biomurph/DINACON_Hummingbird_Heartbeats/2019/HummingBirdHeartbeats_01.JPG

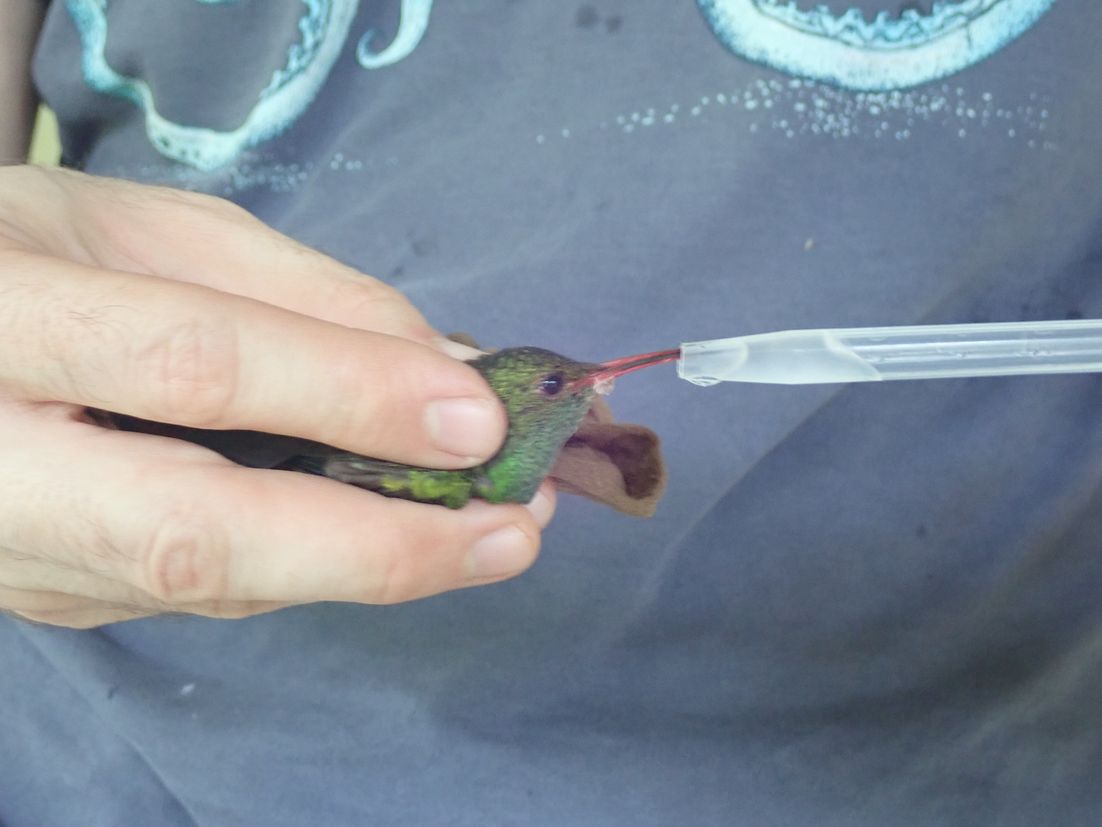
2019/HummingBirdHeartbeats_01.JPG
