biomurph/DINACON_Hummingbird_Heartbeats/2019/HummingBirdHeartbeats_02.JPG

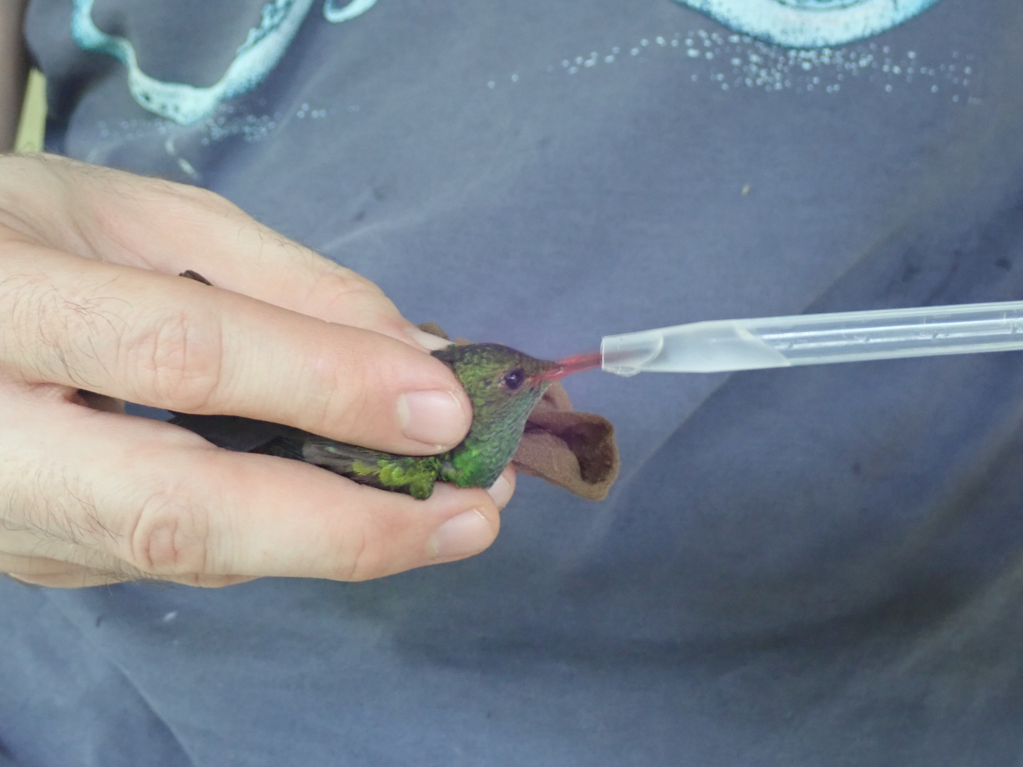
2019/HummingBirdHeartbeats_02.JPG
