biomurph/DINACON_Hummingbird_Heartbeats/2019/HummingBirdHeartbeats_03.JPG

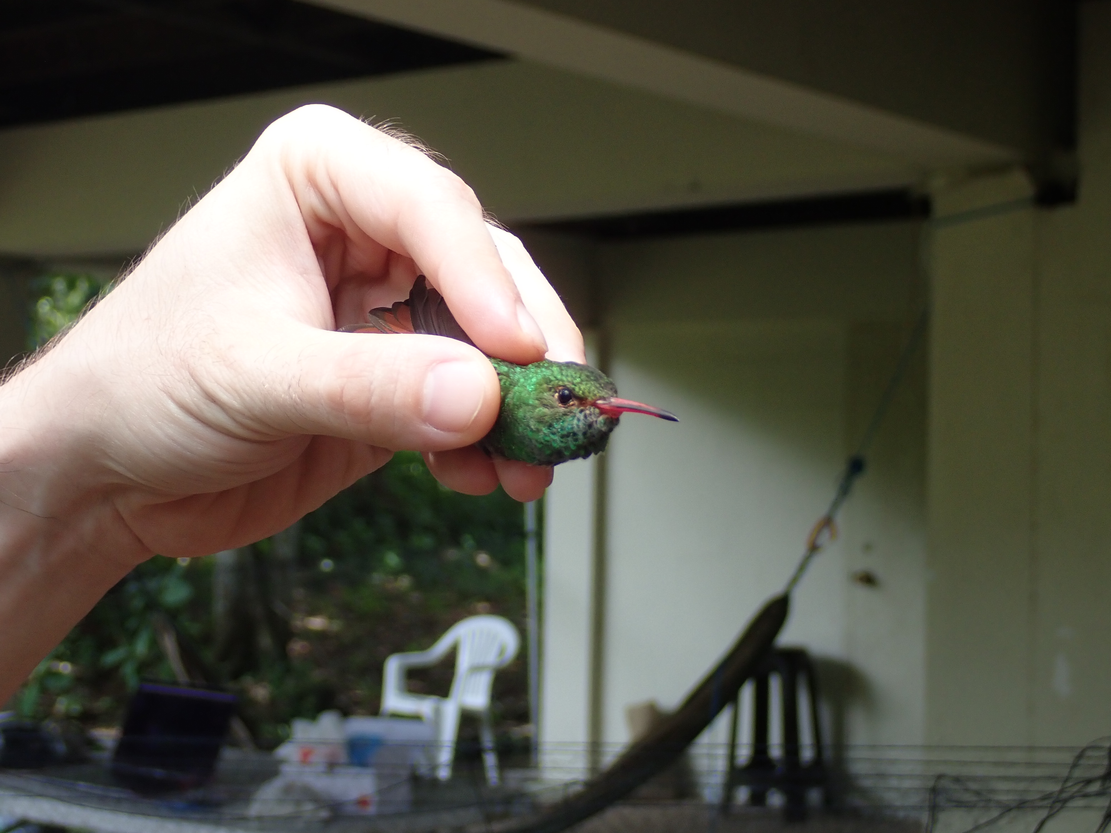
2019/HummingBirdHeartbeats_03.JPG
