biomurph/DINACON_Hummingbird_Heartbeats/2019/HummingBirdHeartbeats_04.JPG

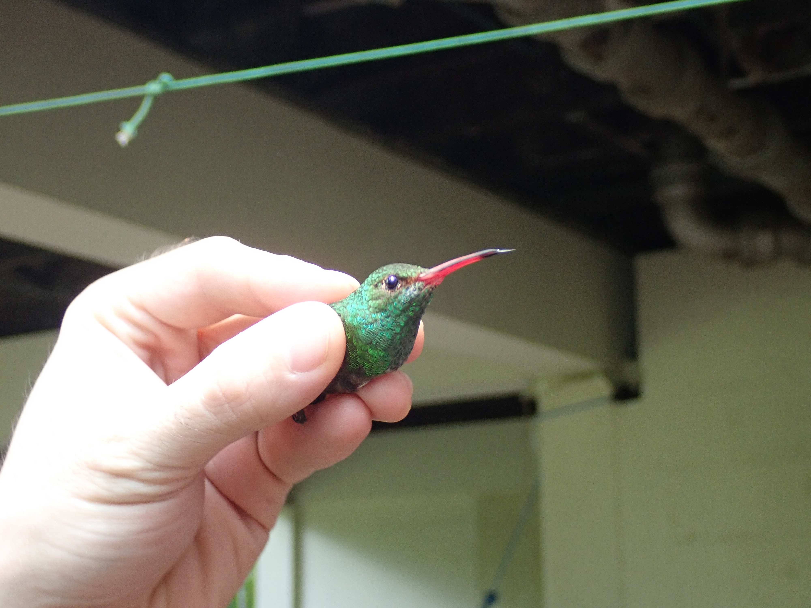
2019/HummingBirdHeartbeats_04.JPG
