biomurph/DINACON_Hummingbird_Heartbeats/2019/HummingBirdHeartbeats_05.JPG

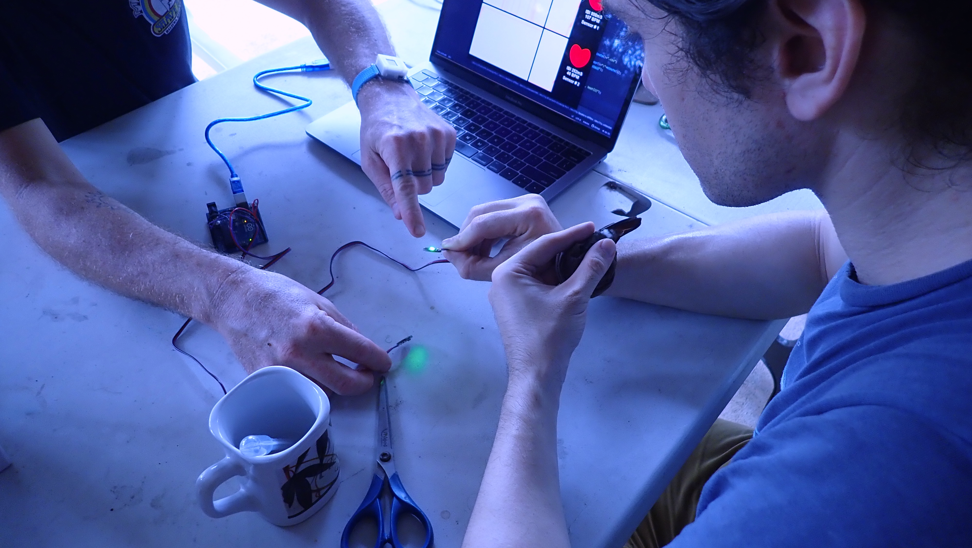
2019/HummingBirdHeartbeats_05.JPG
