biomurph/DINACON_Hummingbird_Heartbeats/2019/HummingBirdHeartbeats_09.JPG

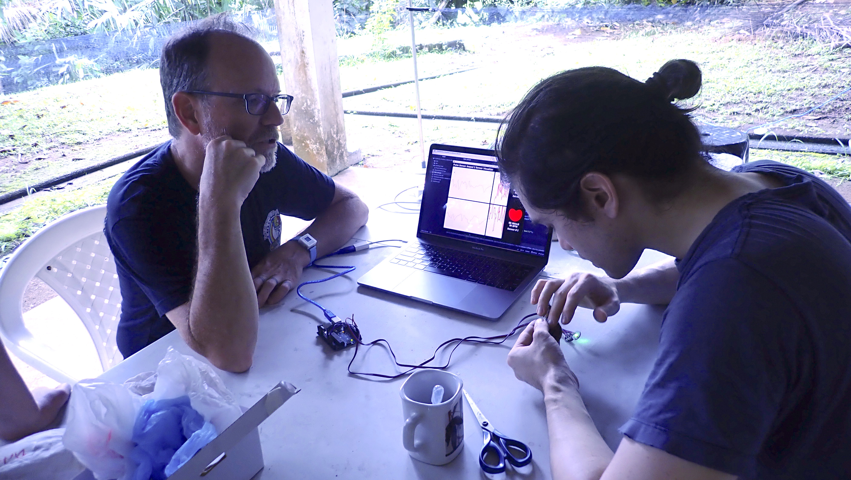
2019/HummingBirdHeartbeats_09.JPG
