biomurph/DINACON_Hummingbird_Heartbeats/2019/HummingBirdHeartbeats_10.JPG

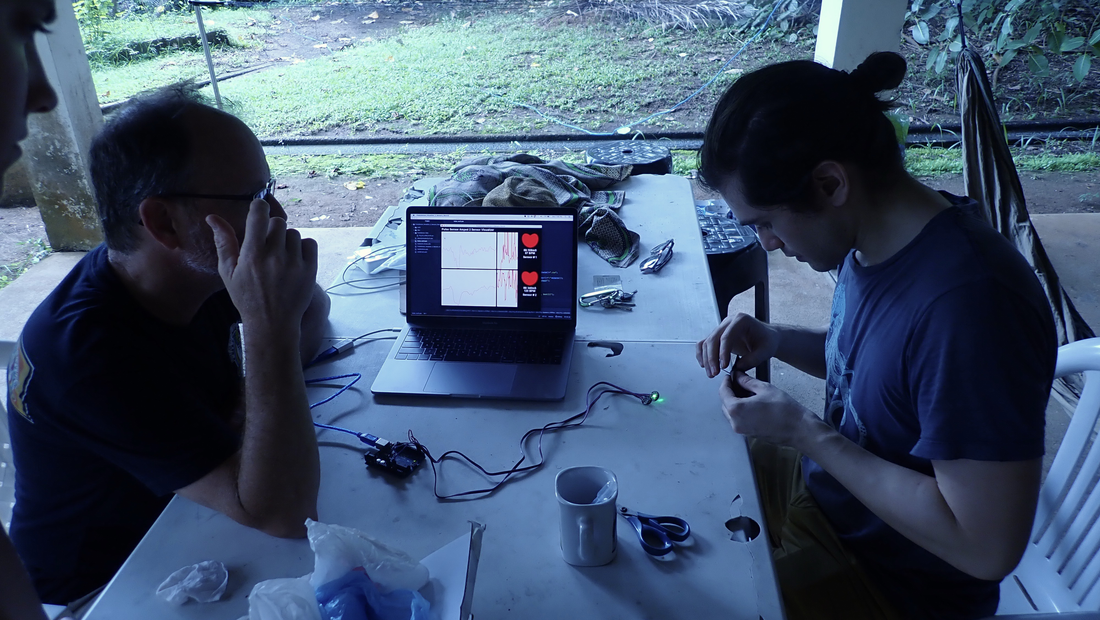
2019/HummingBirdHeartbeats_10.JPG
