biomurph/DINACON_Hummingbird_Heartbeats/2019/HummingBirdHeartbeats_12.JPG

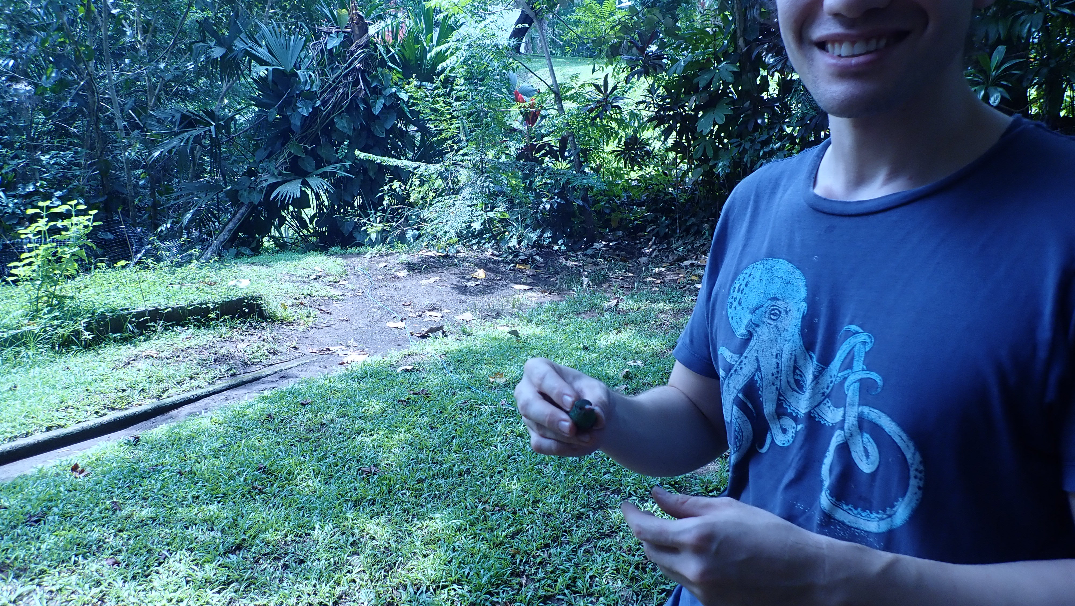
2019/HummingBirdHeartbeats_12.JPG
