biomurph/DINACON_Hummingbird_Heartbeats/2019/HummingBirdHeartbeats_15.JPG

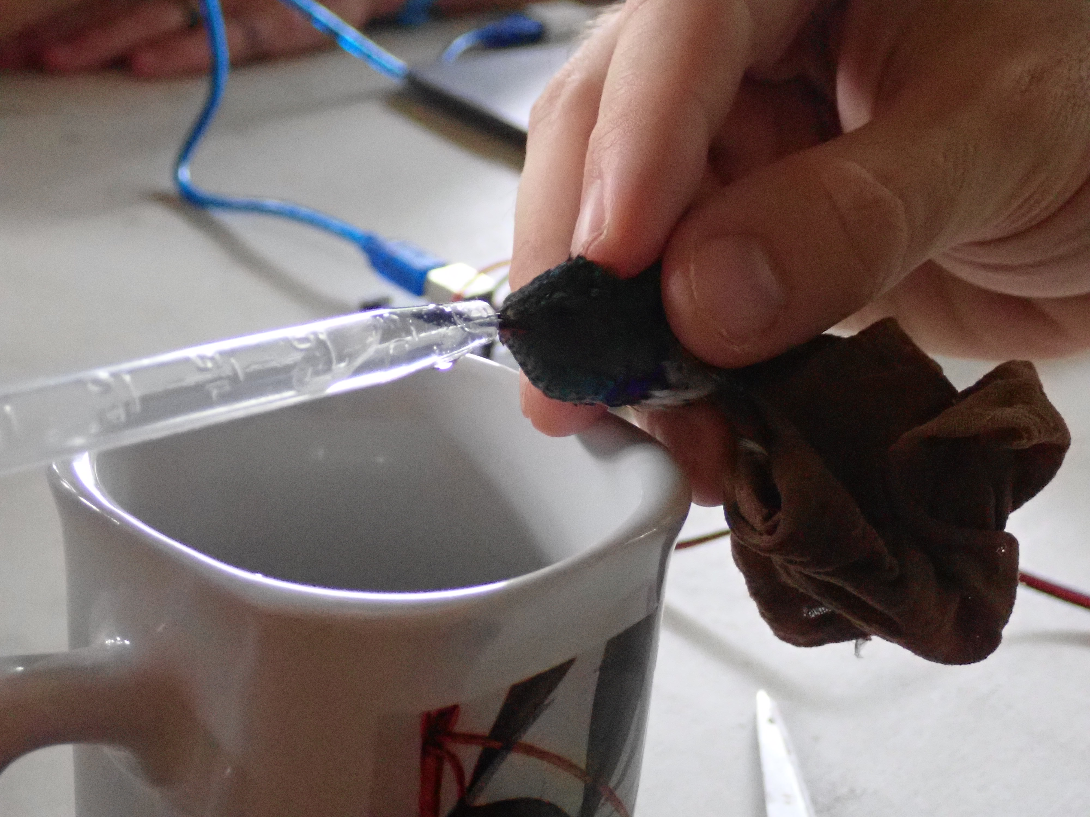
2019/HummingBirdHeartbeats_15.JPG
