biomurph/DINACON_Hummingbird_Heartbeats/2019/HummingBirdHeartbeats_16.JPG

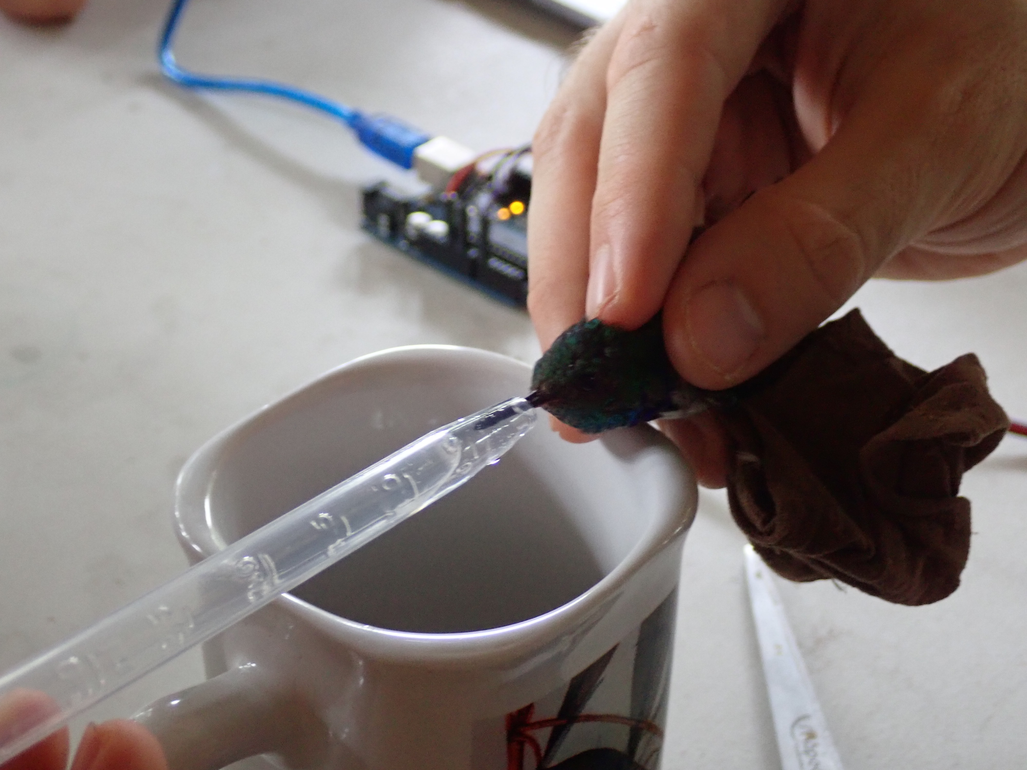
2019/HummingBirdHeartbeats_16.JPG
