biomurph/DINACON_Hummingbird_Heartbeats/2019/HummingBirdHeartbeats_19.JPG

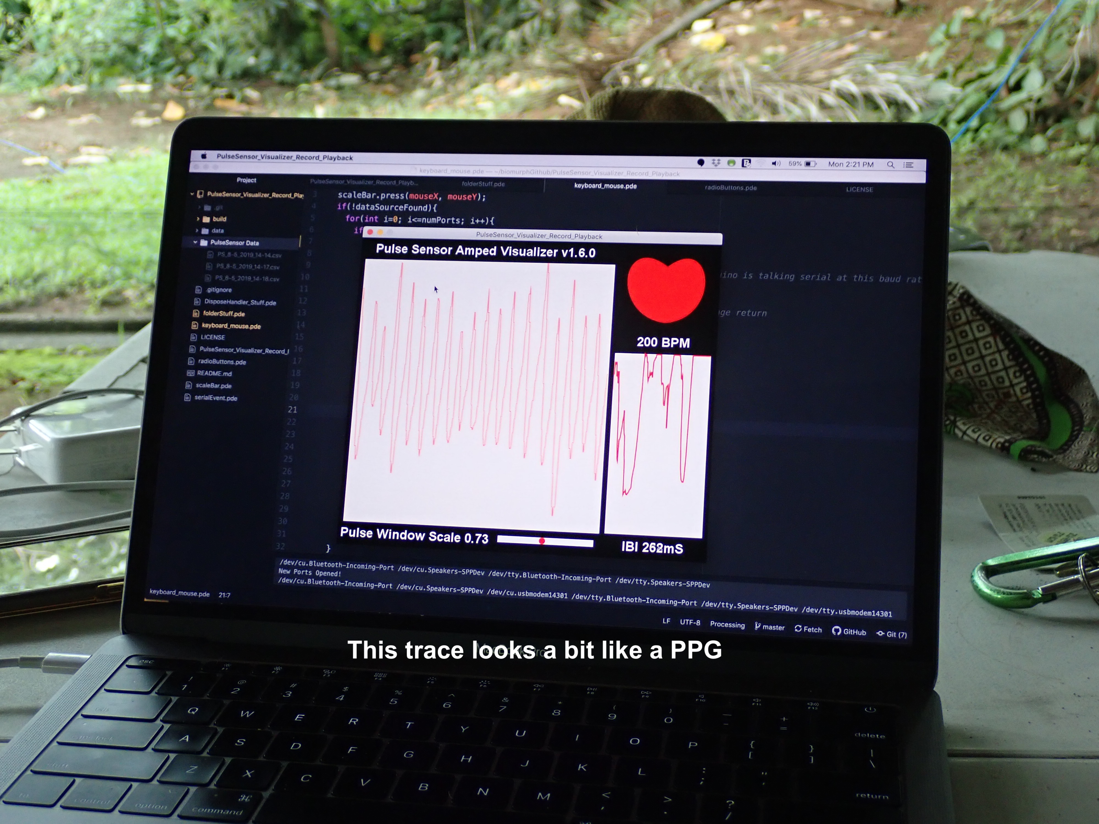
2019/HummingBirdHeartbeats_19.JPG
