biomurph/DINACON_Hummingbird_Heartbeats/2019/HummingBirdHeartbeats_20.JPG

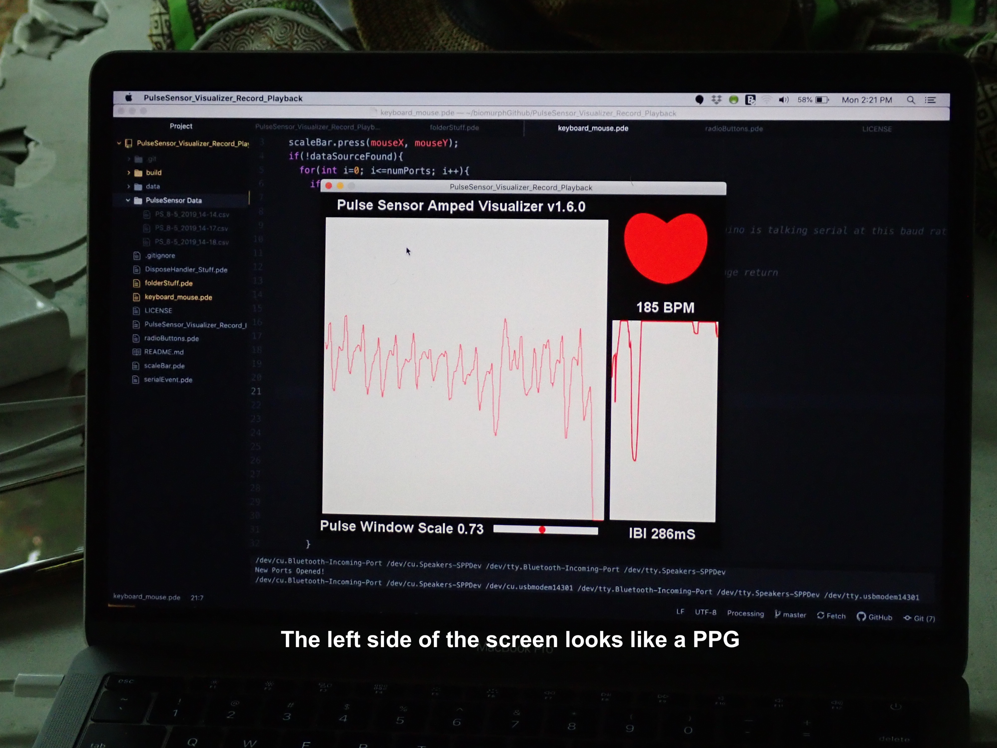
2019/HummingBirdHeartbeats_20.JPG
