biomurph/DINACON_Hummingbird_Heartbeats/2019/HummingBirdHeartbeats_22.JPG

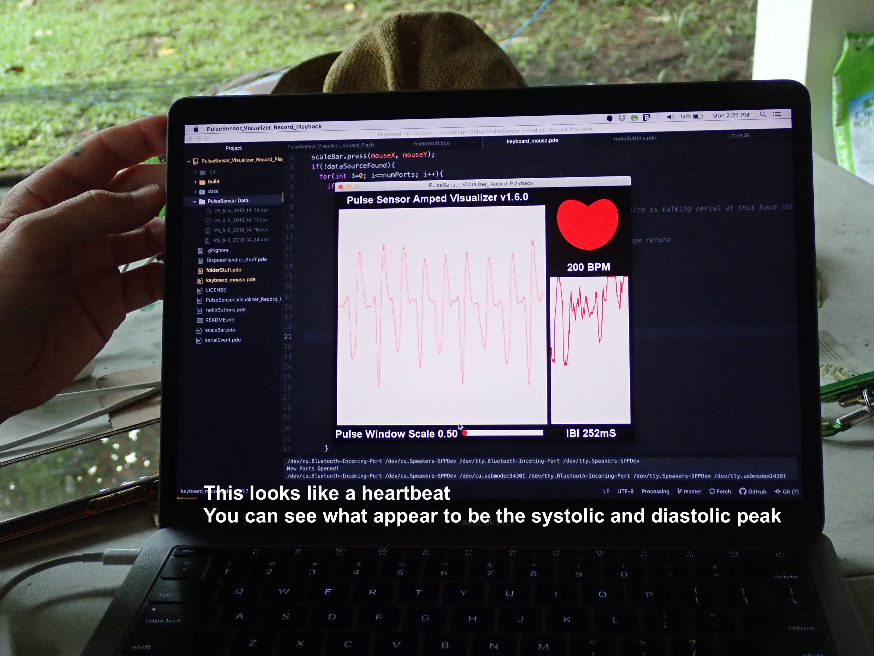
2019/HummingBirdHeartbeats_22.JPG
