biomurph/DINACON_Hummingbird_Heartbeats/2019/IMG_20190805_141204.jpg

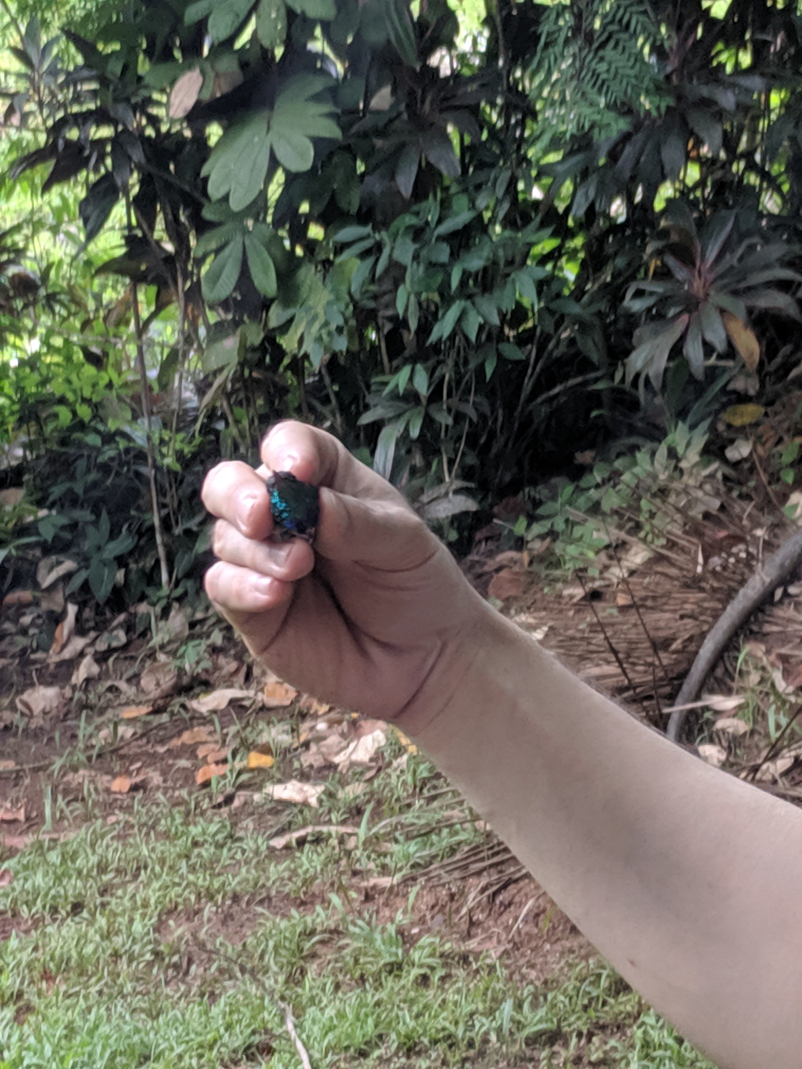
2019/IMG_20190805_141204.jpg
