biomurph/DINACON_Hummingbird_Heartbeats/2022/Data/1st_attempts/boto_01.png

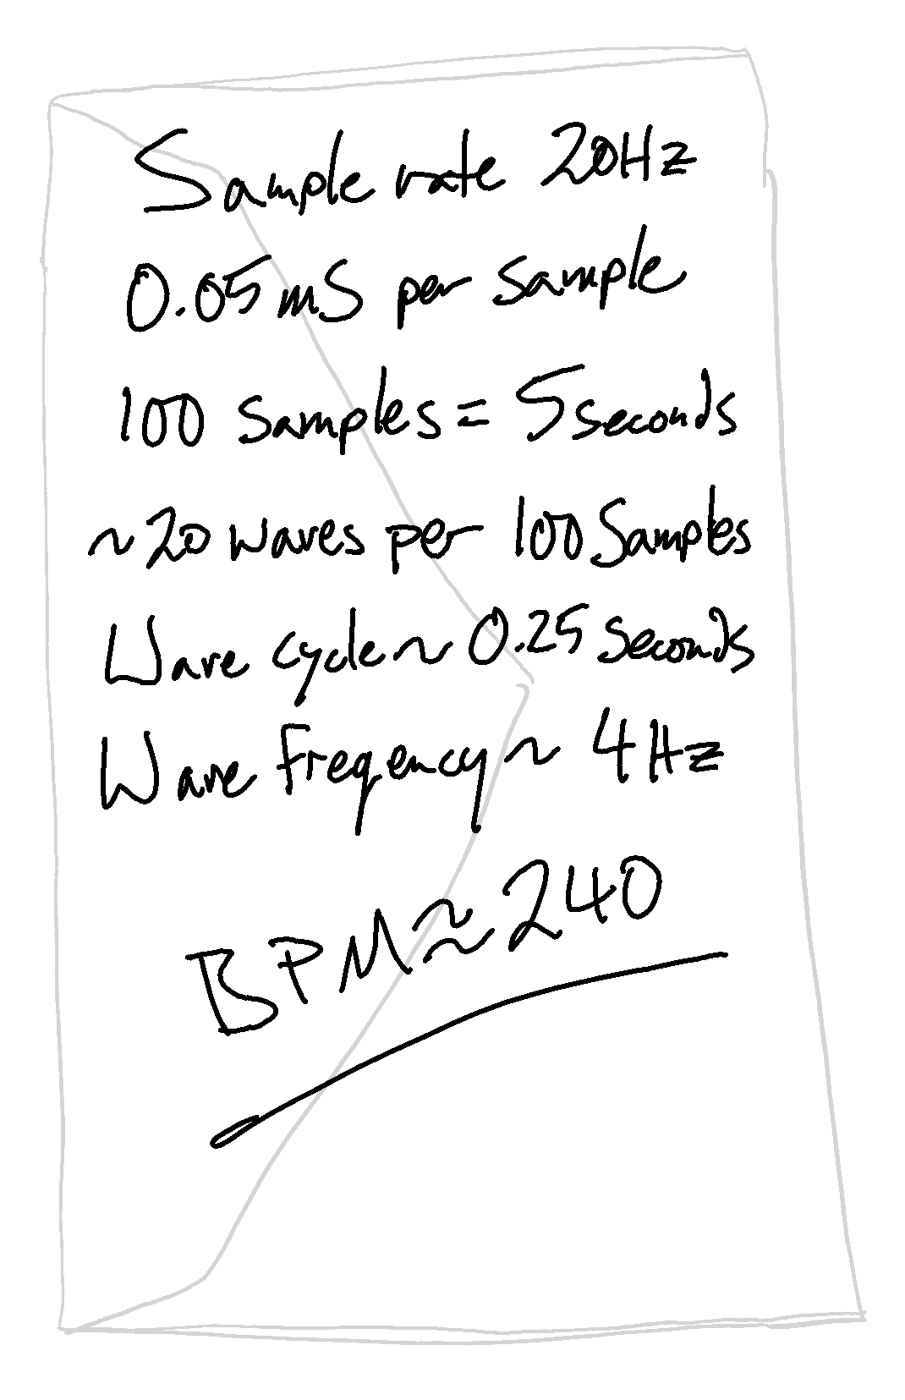
2022/Data/1st_attempts/boto_01.png
