biomurph/DINACON_Hummingbird_Heartbeats/2022/Data/1st_attempts/PulseSensor_glue_Accel.png

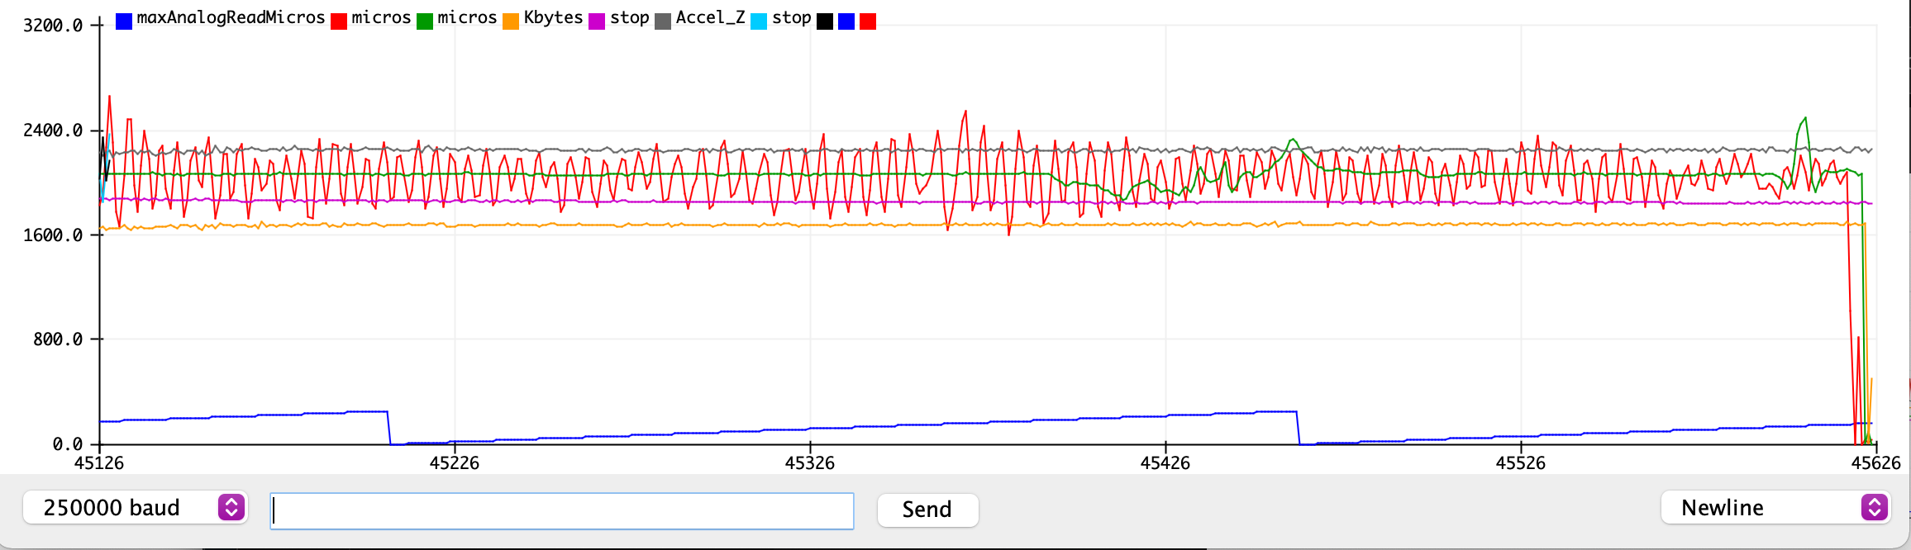
2022/Data/1st_attempts/PulseSensor_glue_Accel.png
