biomurph/DINACON_Hummingbird_Heartbeats/2022/Data/1st_attempts/PulseSensor_only.png

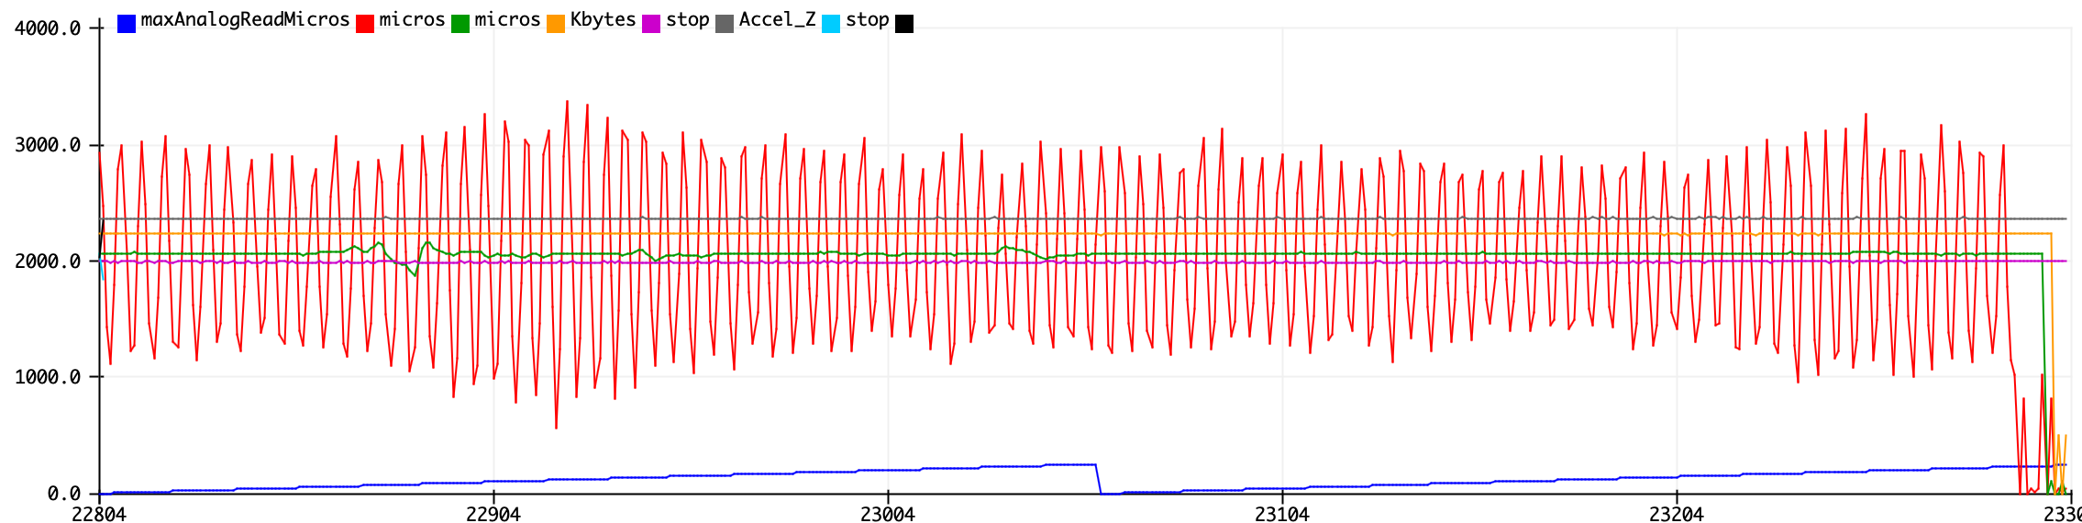
2022/Data/1st_attempts/PulseSensor_only.png
