biomurph/DINACON_Hummingbird_Heartbeats/2022/Data/1st_attempts/Very_First_Try.png

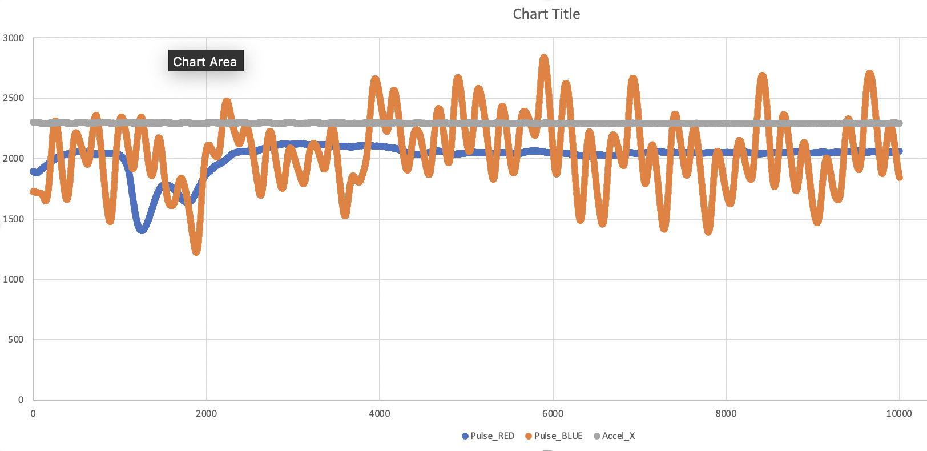
2022/Data/1st_attempts/Very_First_Try.png
