biomurph/DINACON_Hummingbird_Heartbeats/2022/Arduino/humm_beat_sensor_01/button_stuph.ino

boolean getButtonState(){
  buttonValue = digitalRead(BUTTON_PIN);
  if(buttonValue != lastButtonValue){
    delay(10);
    buttonValue = digitalRead(BUTTON_PIN);
    if(buttonValue != lastButtonValue){
      if(buttonValue == LOW){ // she's pressed!
        Serial.println(F("\nbutton press\n"));
        isRunning = true;
        fadeLED(millis());
      }
    }
    lastButtonValue = buttonValue;
  }
  return isRunning;
}
